greygoo/Meshed-Banana/images/case/Meshed_Banana_back.jpg

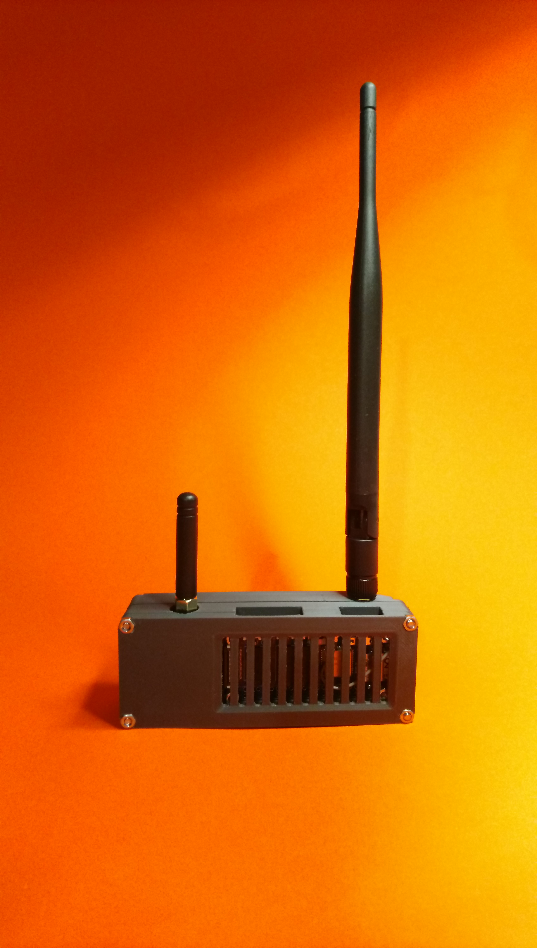
images/case/Meshed_Banana_back.jpg
