greygoo/Meshed-Banana/images/case/Meshed_Banana_front.jpg

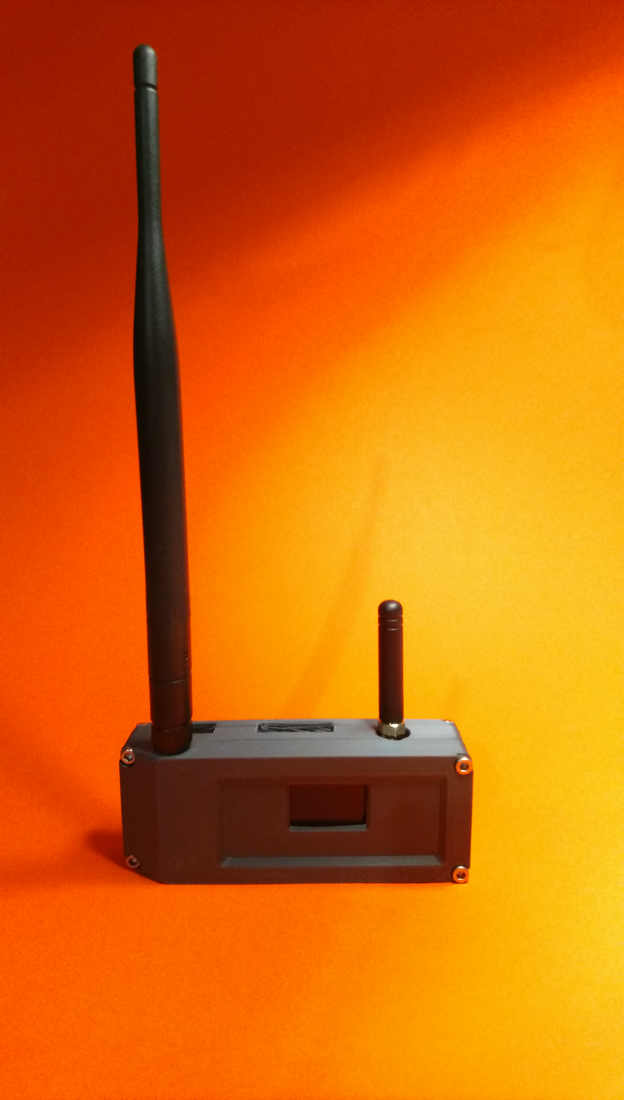
images/case/Meshed_Banana_front.jpg
